Hanz-Tech/yrm100-rfid-flipper-board/image/5.JPG

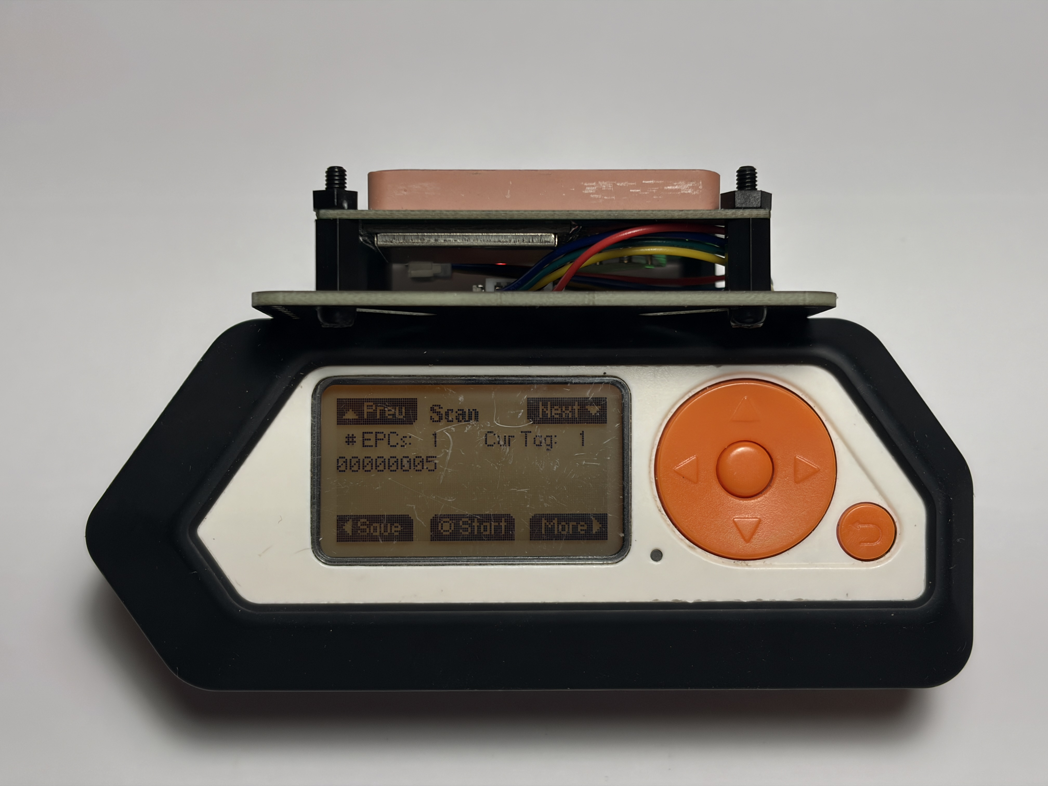
image/5.JPG
