Hanz-Tech/yrm100-rfid-flipper-board/image/6.jpg

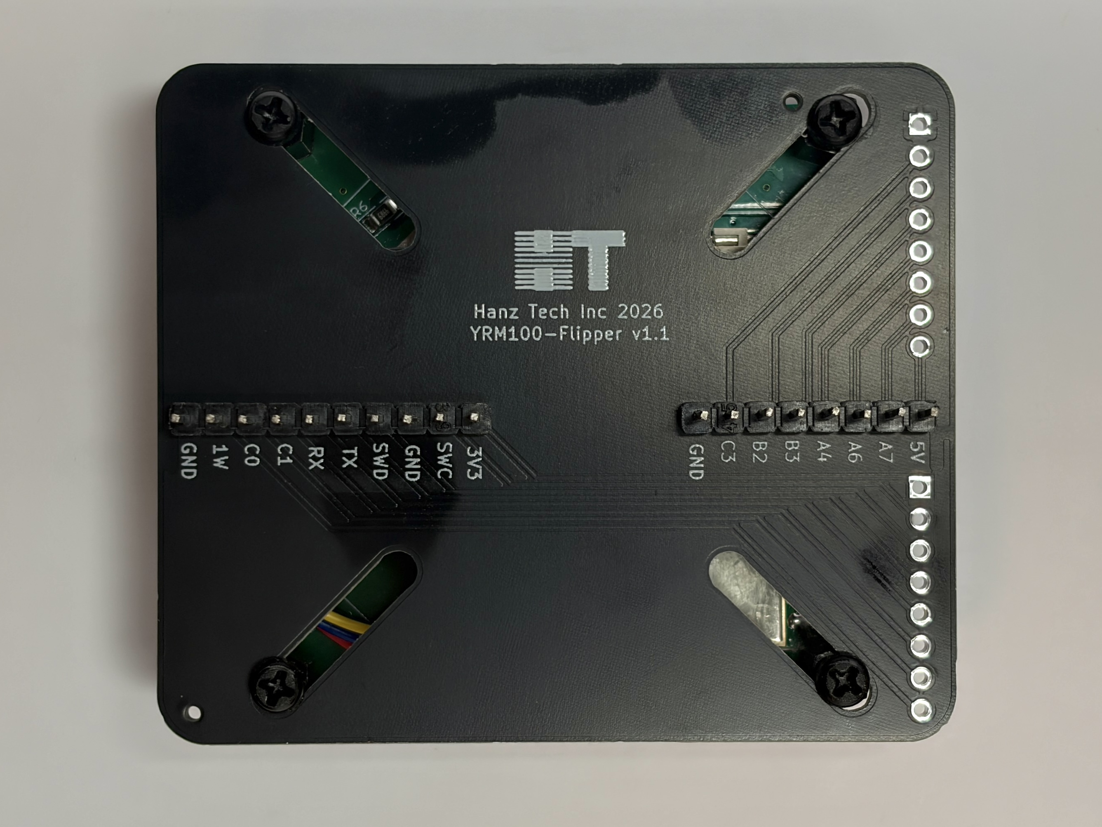
image/6.jpg
